SarvaarthN/ESP32_WorldClock_Alarm/PCB/12HrClock_PCB/12HrClock_PCB.kicad_pcb

## KiCad design PCB/12HrClock_PCB/12HrClock_PCB.kicad_pcb (2026-01-28)

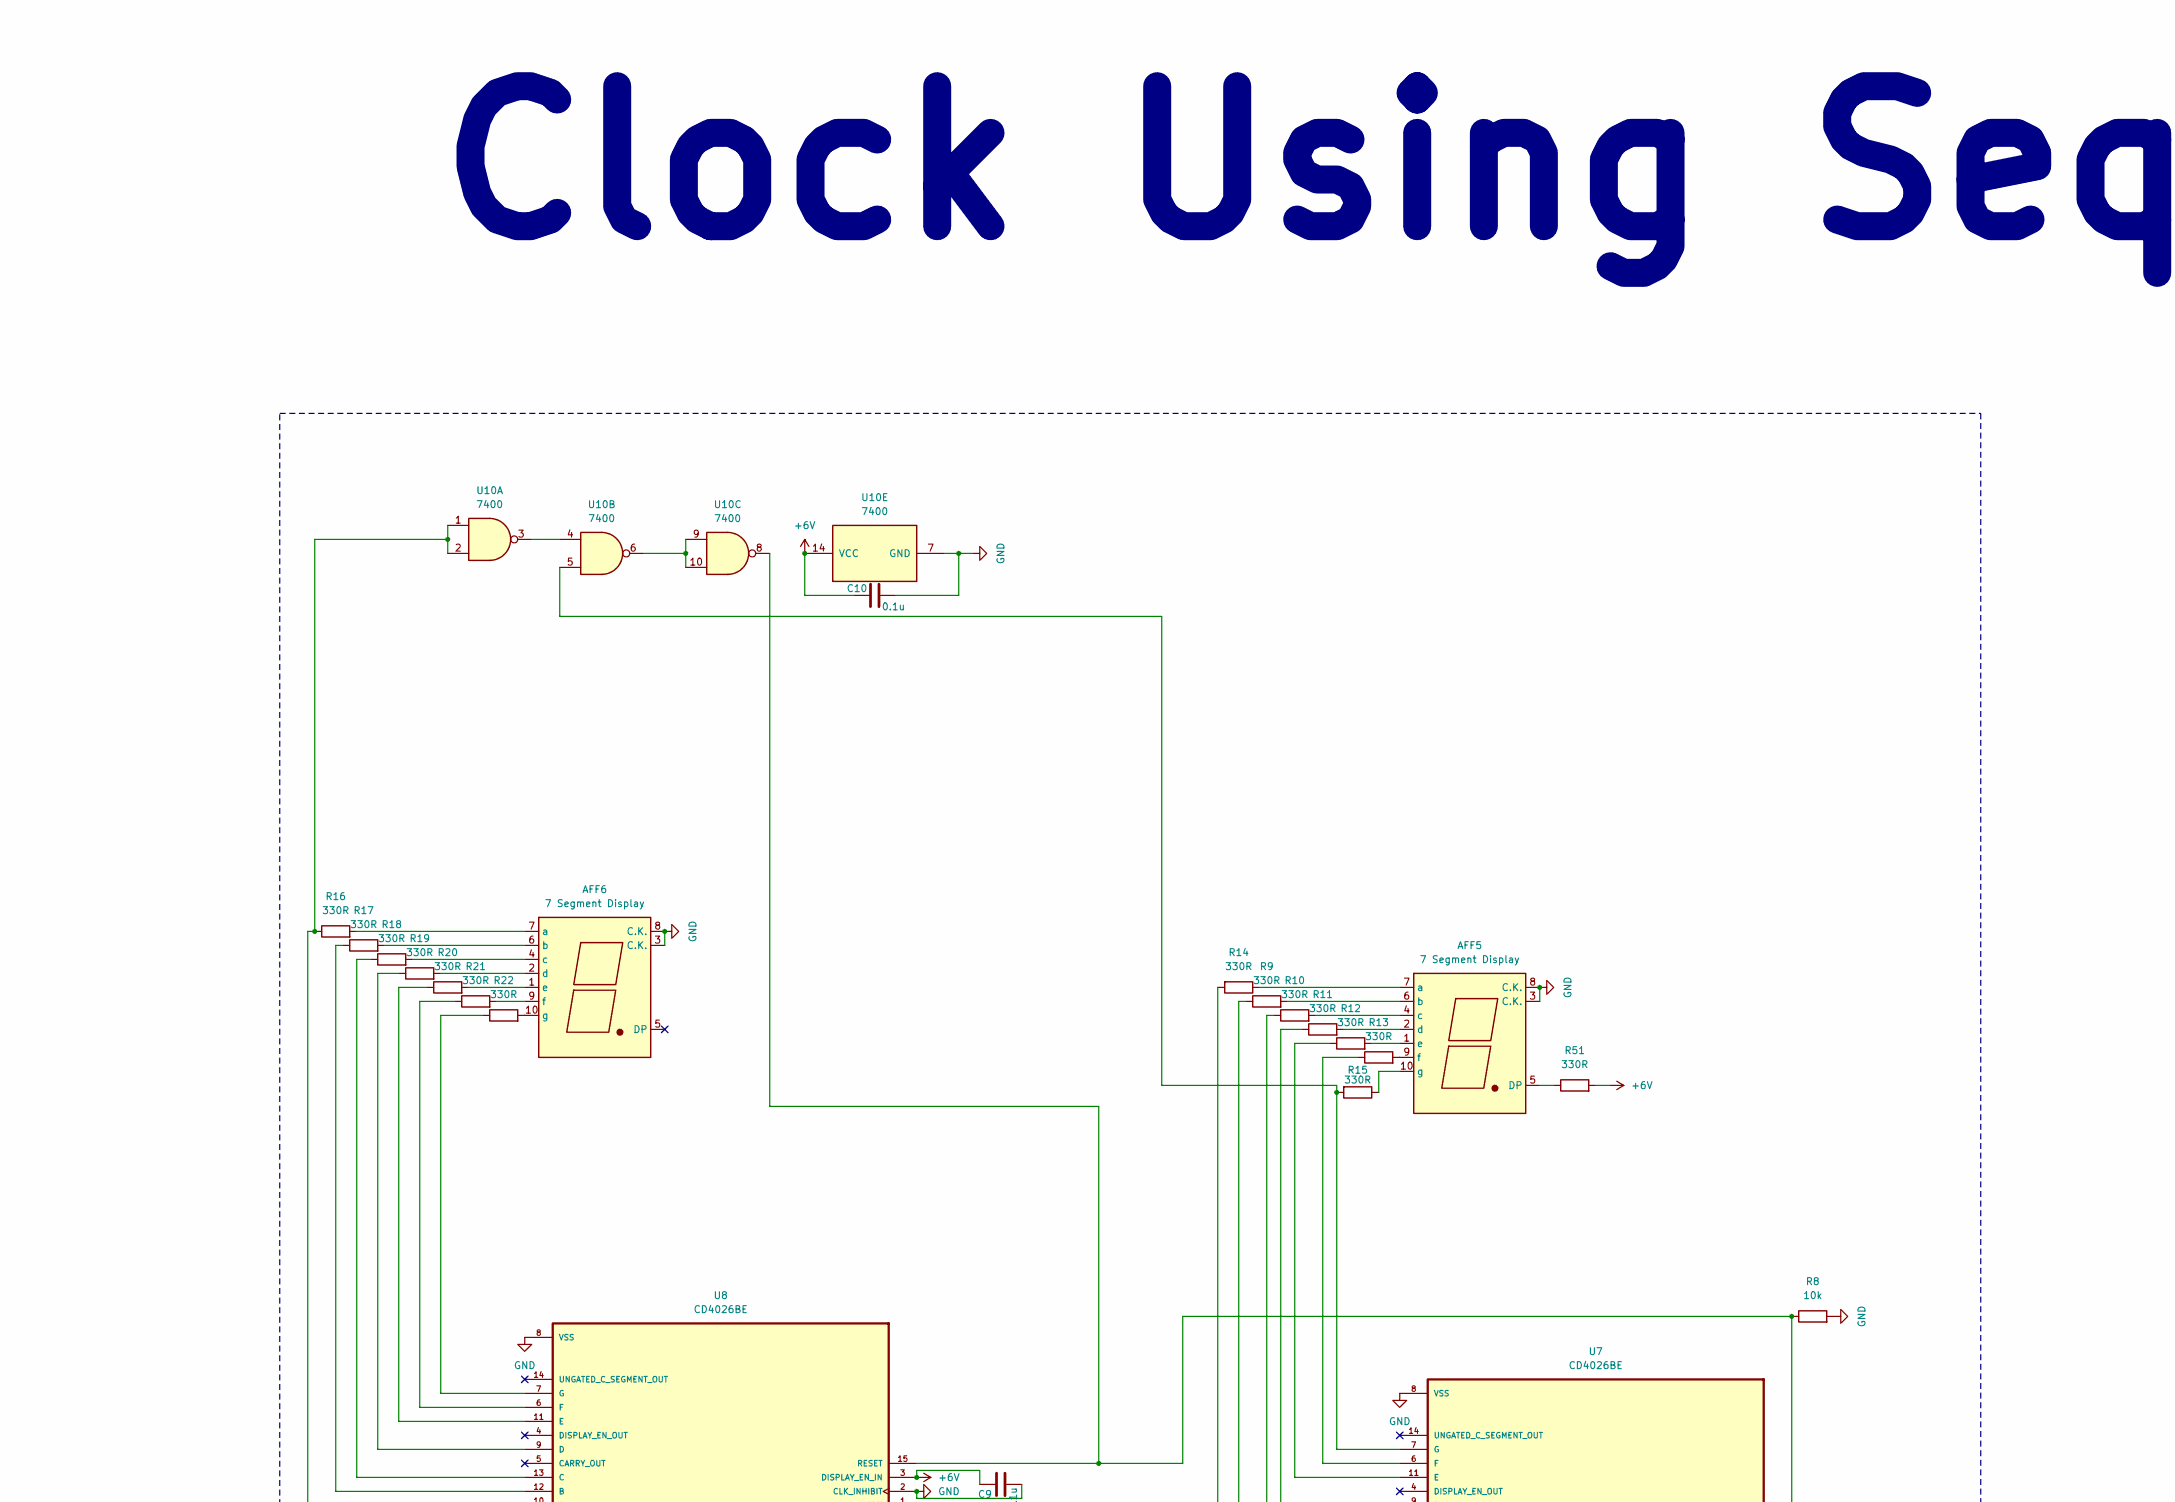
[picture p11: schematic 12HrClock_PCB.kicad_sch, part in row 1, column 1]

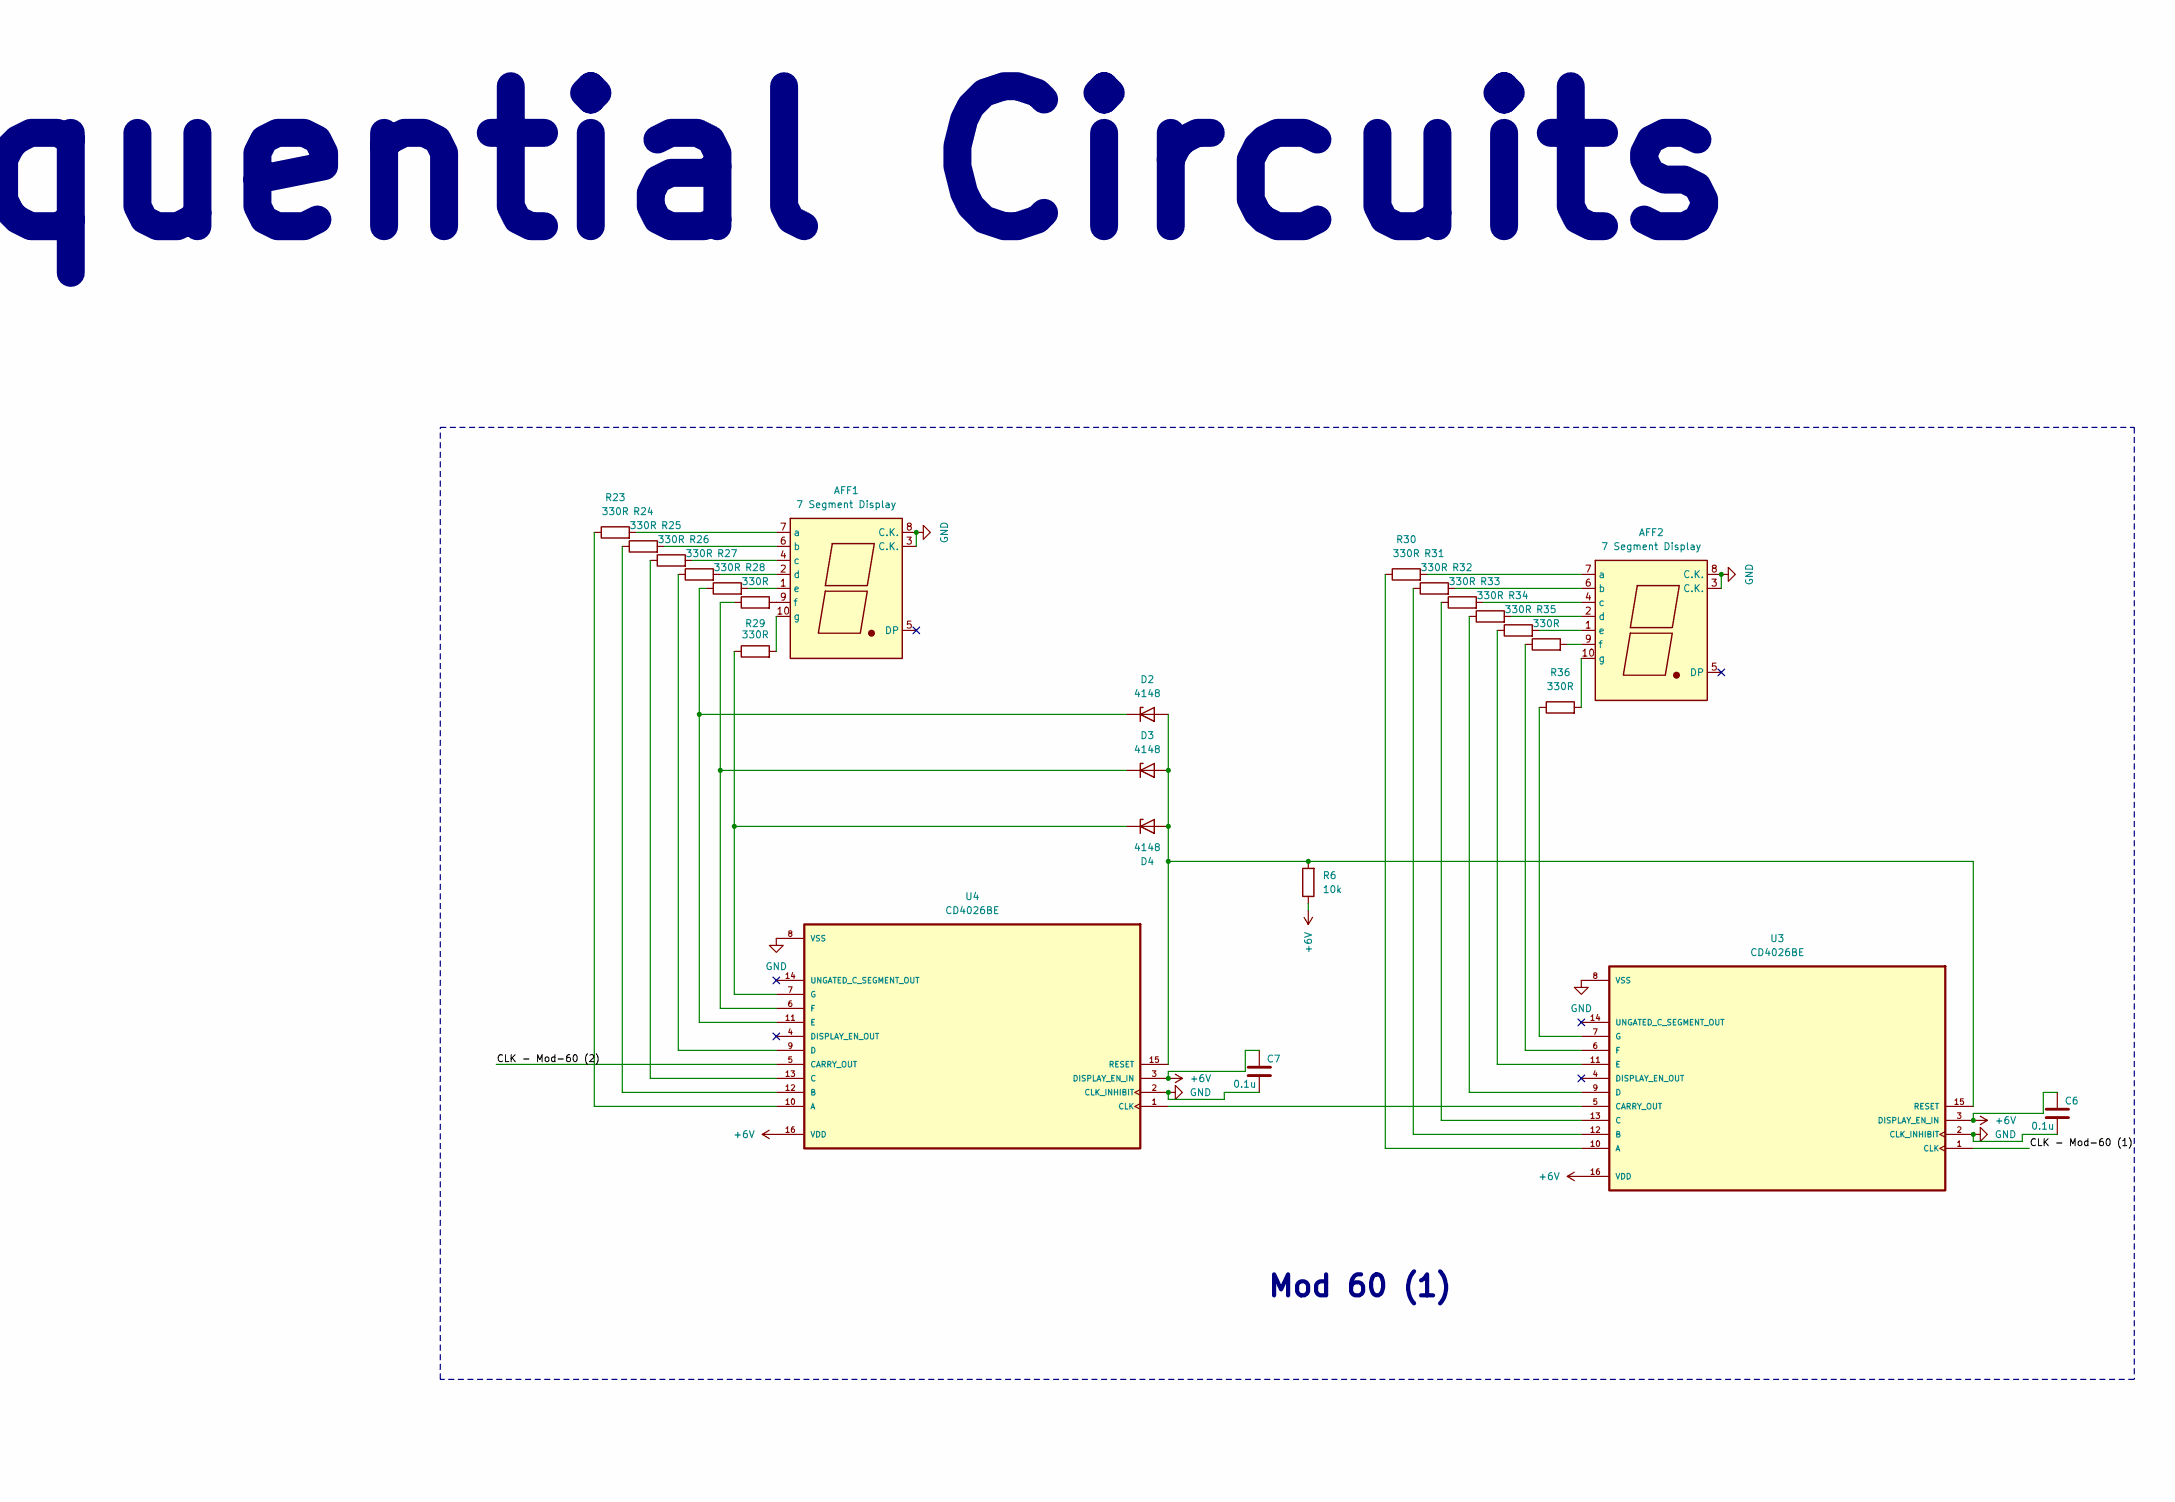
[picture p12: schematic 12HrClock_PCB.kicad_sch, part in row 1, column 2]

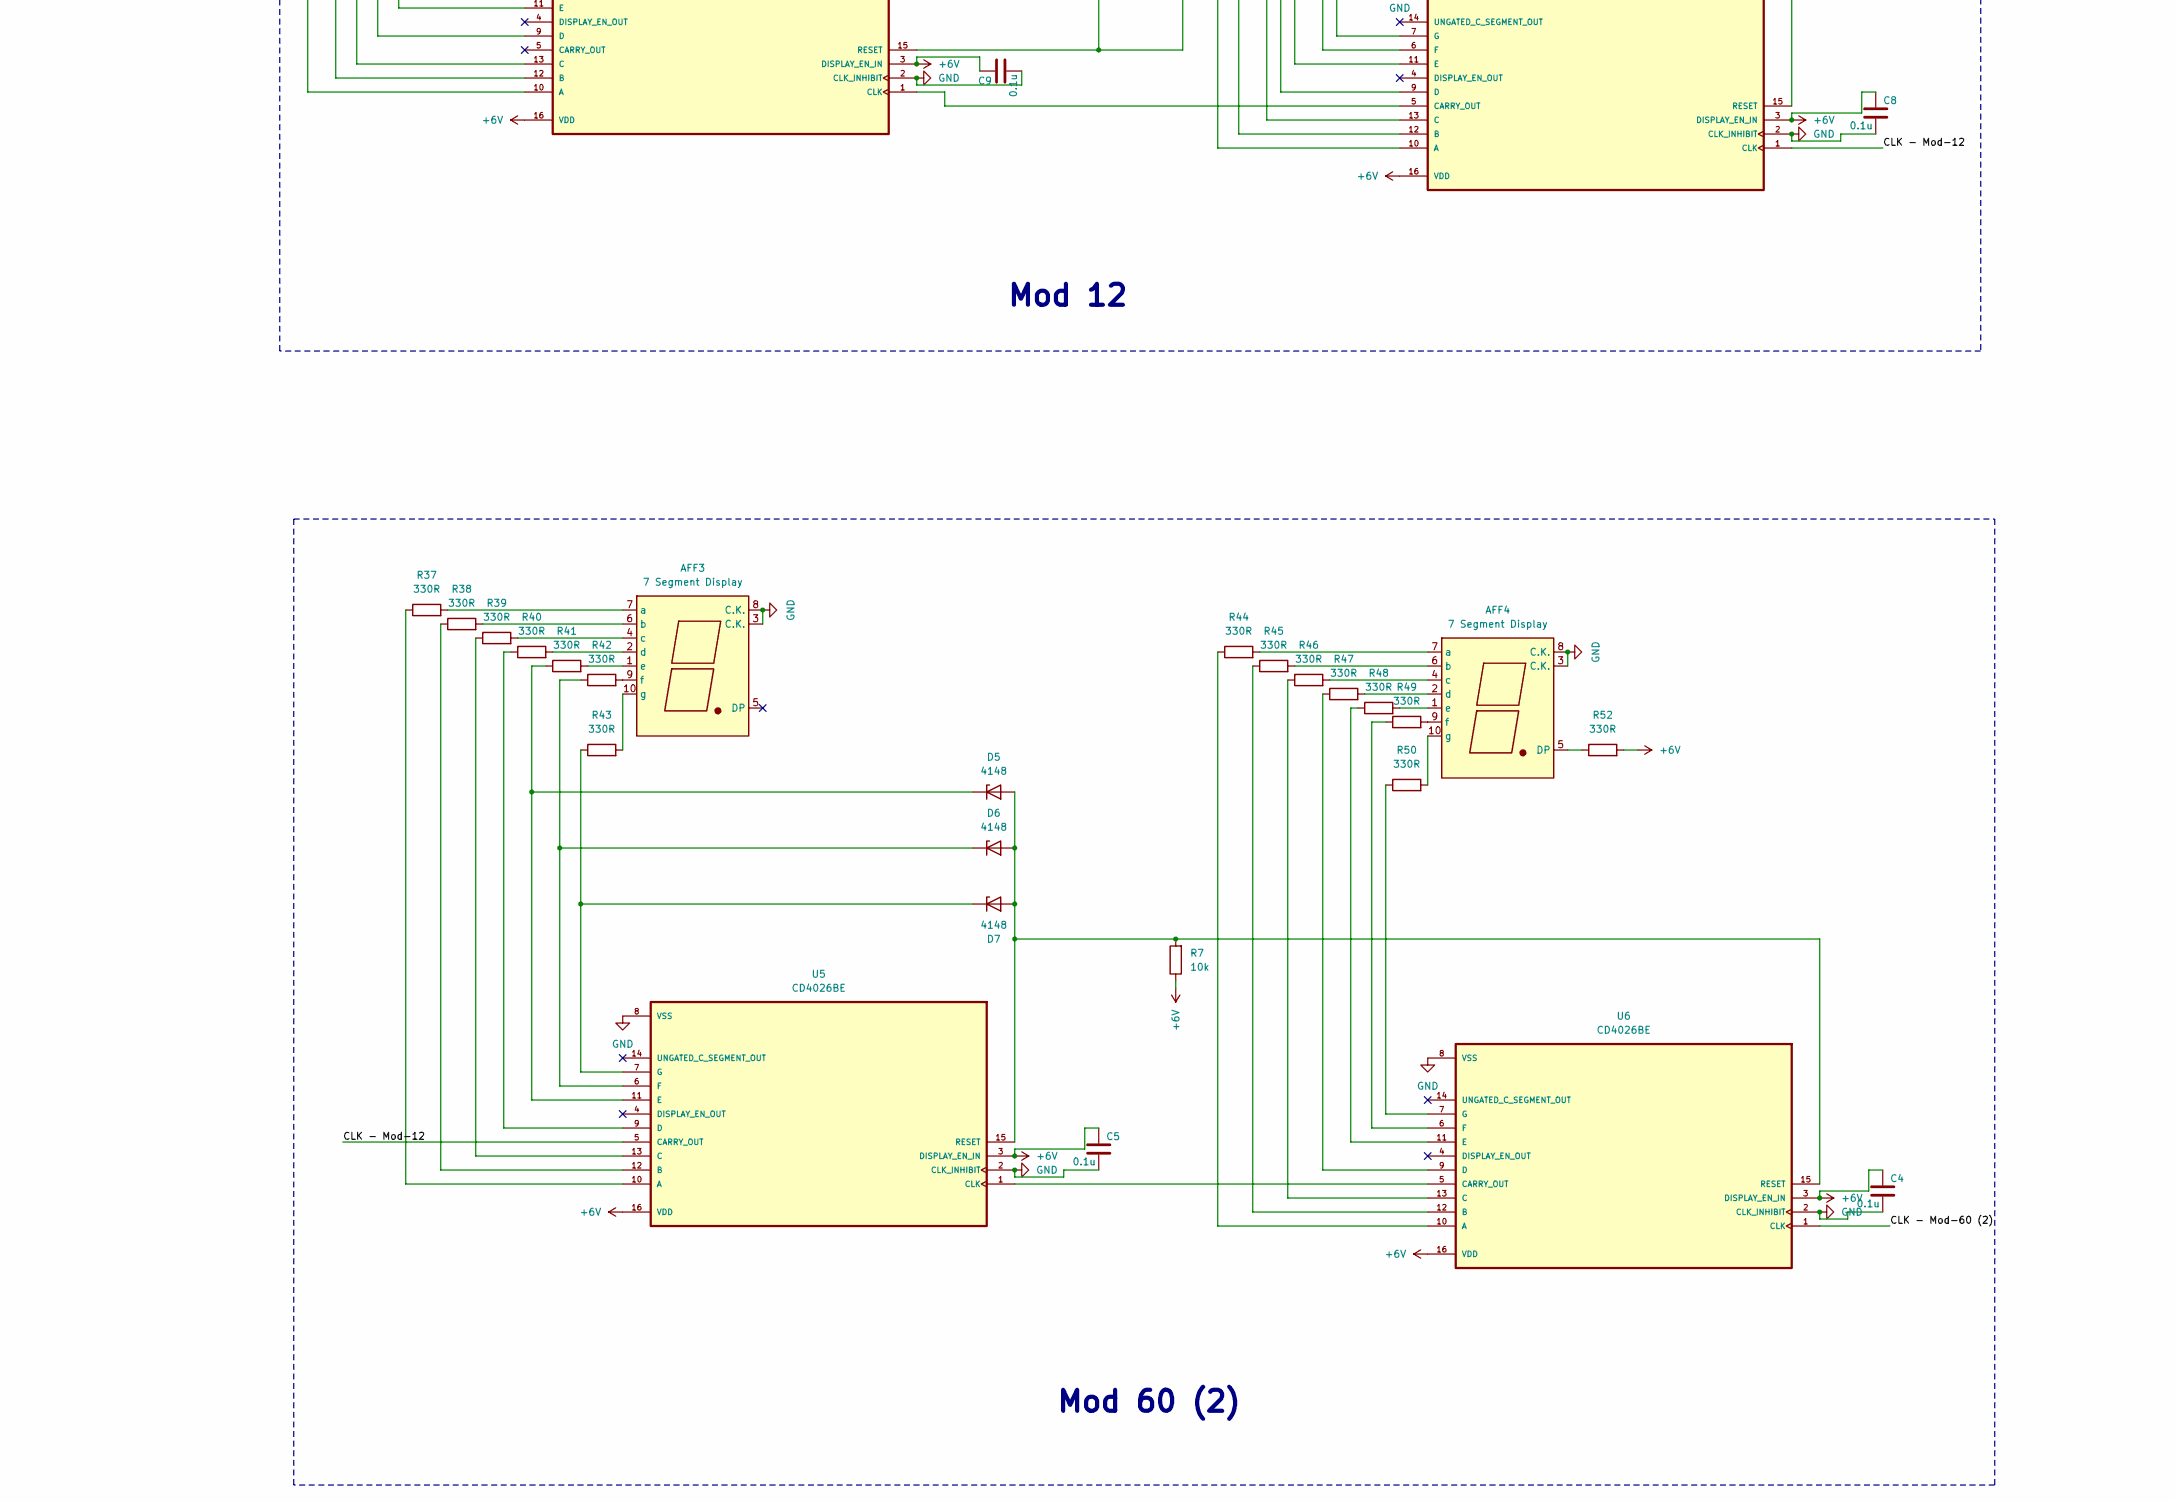
[picture p13: schematic 12HrClock_PCB.kicad_sch, part in row 2, column 1]

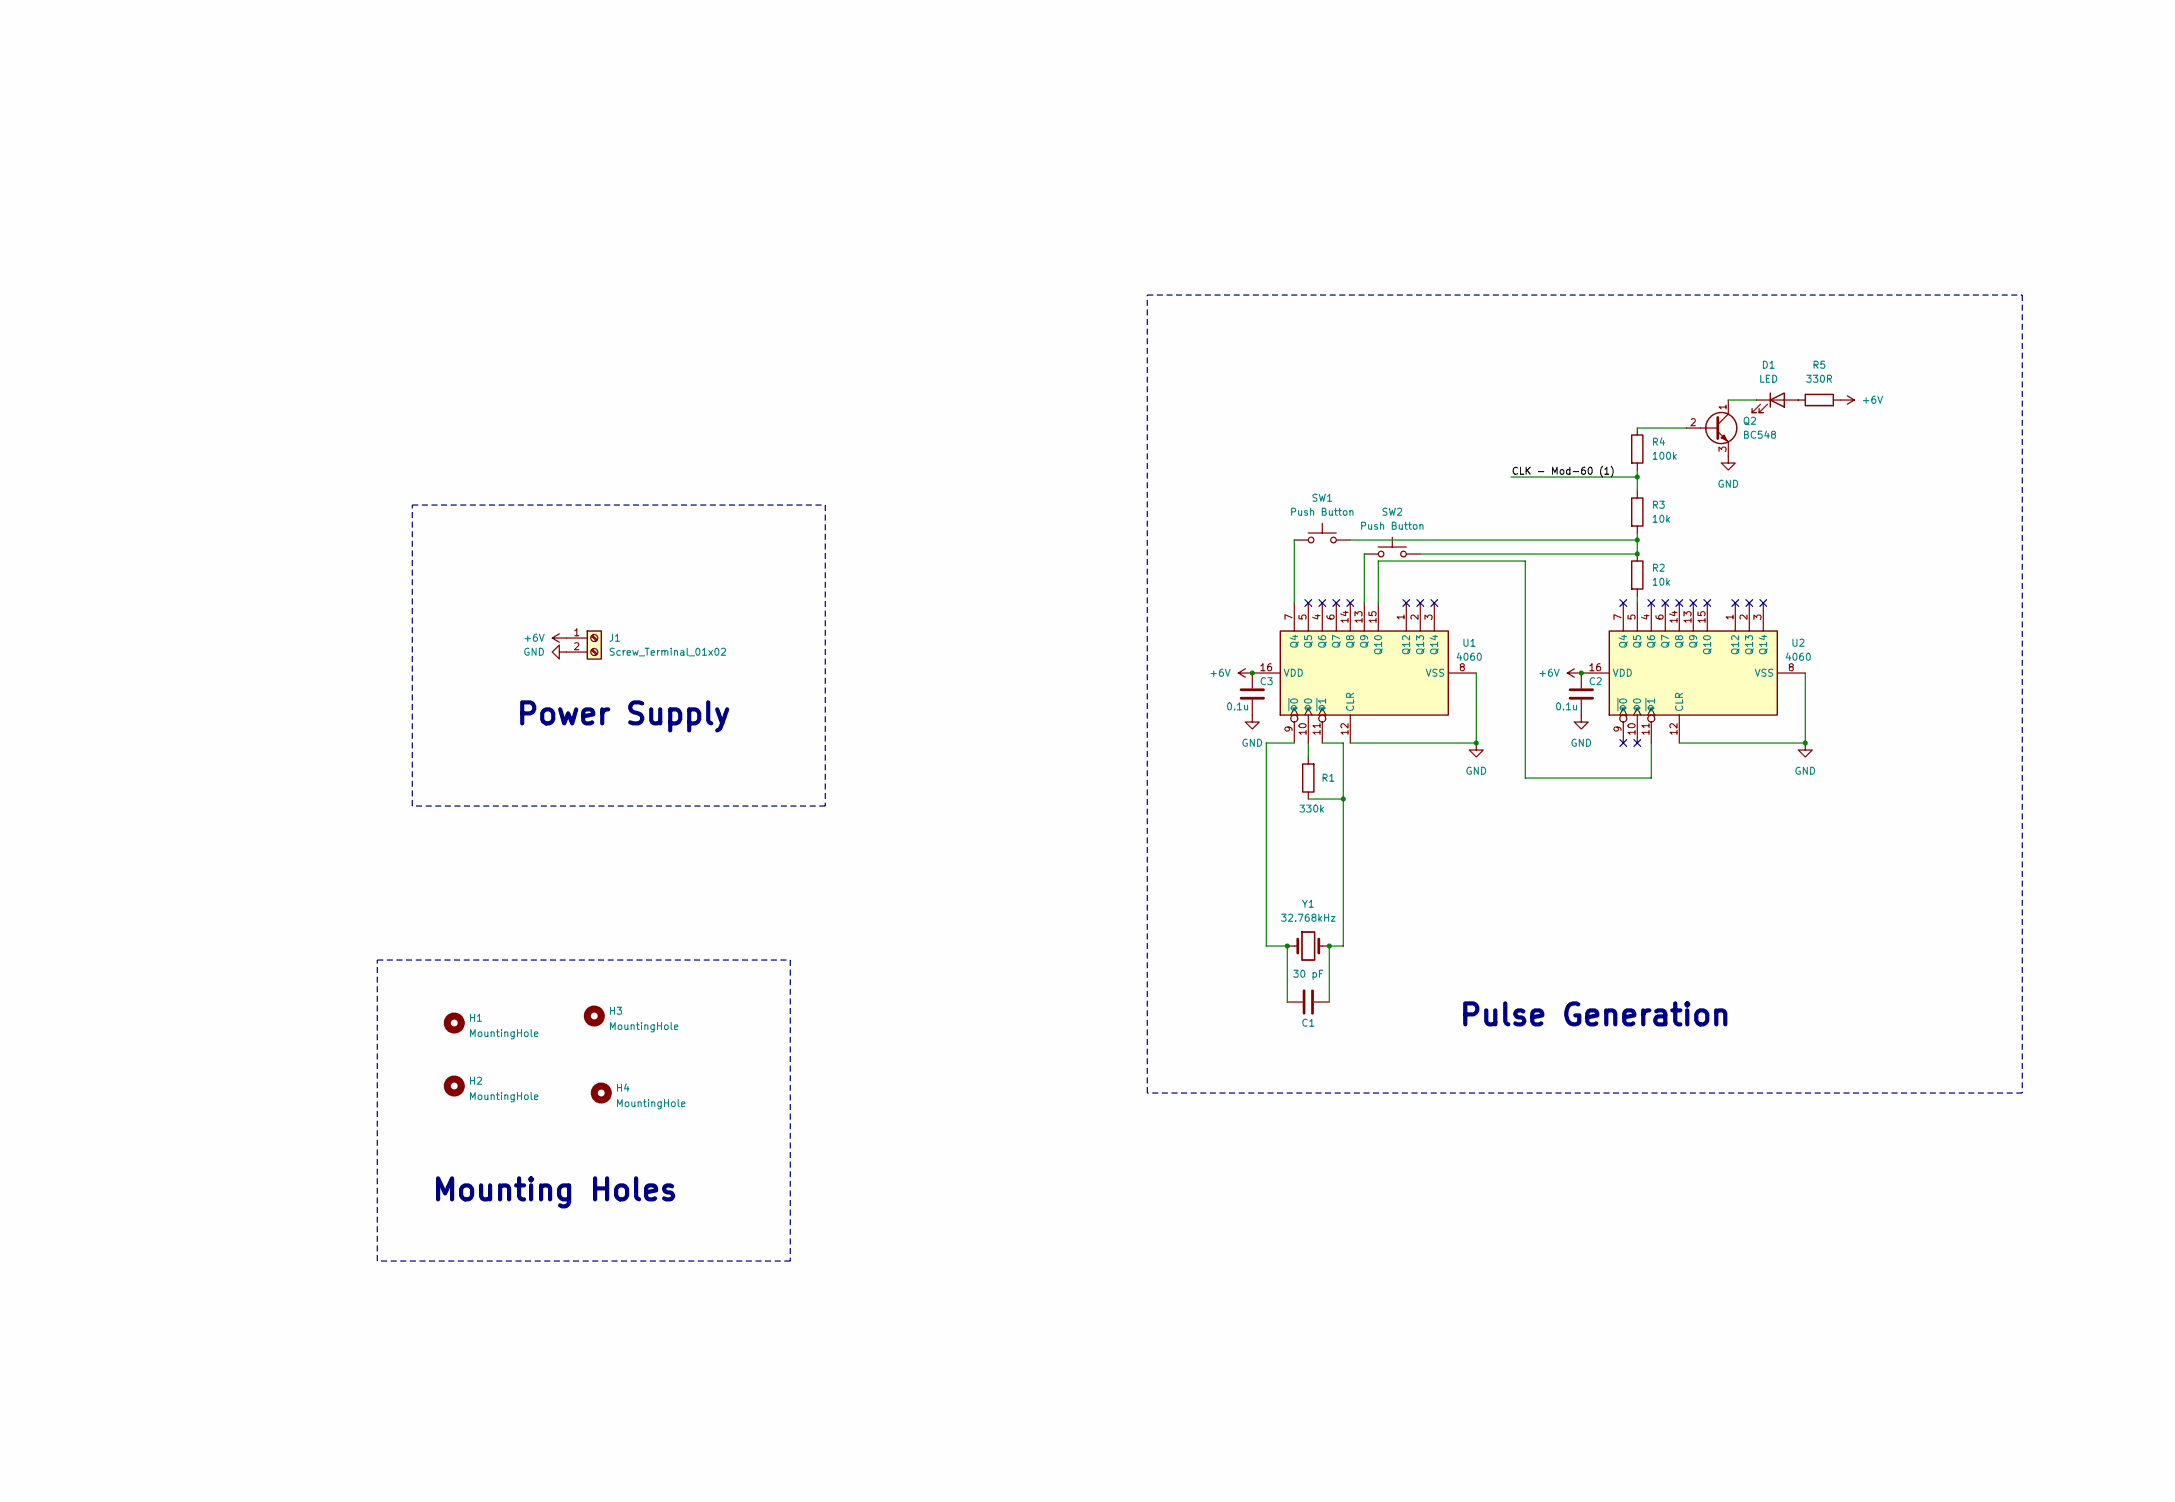
[picture p14: schematic 12HrClock_PCB.kicad_sch, part in row 2, column 2]

Parts:
AFF1, AFF2, AFF3, AFF4, AFF5, AFF6: 7 Segment Display; 7SegmentLED_LTS6760_LTS6780
C1: 30 pF; C_0805_2012Metric_Pad1.18x1.45mm_HandSolder
C2, C3, C4, C5, C6, C7, C8, C9, C10: 0.1u; C_0805_2012Metric_Pad1.18x1.45mm_HandSolder
D1: LED; LED_0805_2012Metric_Pad1.15x1.40mm_HandSolder
D2, D3, D4, D5, D6, D7: 4148; D_DO-35_SOD27_P7.62mm_Horizontal
H1, H2, H3, H4: MountingHole; MountingHole_3.2mm_M3
J1: Screw_Terminal_01x02; TerminalBlock_Phoenix_PT-1,5-2-5.0-H_1x02_P5.00mm_Horizontal
Q2: BC548; TO-92_Inline
R1: 330k; R_0805_2012Metric_Pad1.20x1.40mm_HandSolder
R2, R3, R6, R7, R8: 10k; R_0805_2012Metric_Pad1.20x1.40mm_HandSolder
R4: 100k; R_0805_2012Metric_Pad1.20x1.40mm_HandSolder
R5, R9, R10, R11, R12, R13, R14, R15, R16, R17, R18, R19, R20, R21, R22, R23, R24, R25, R26, R27, R28, R29, R30, R31, R32, R33, R34, R35, R36, R37, R38, R39, R40, R41, R42, R43, R44, R45, R46, R47, R48, R49, R50, R51, R52: 330R; R_0805_2012Metric_Pad1.20x1.40mm_HandSolder
SW1, SW2: Push Button; SW_PUSH_6mm
U1, U2: 4060; DIP-16_W7.62mm_LongPads
U3, U4, U5, U6, U7, U8: CD4026BE; DIP-16_W7.62mm_LongPads
U10: 7400; DIP-14_W7.62mm_LongPads
Y1: 32.768kHz; Crystal_DS10_D1.0mm_L4.3mm_Vertical

Connections:
+6V: C2.1, C3.1, C4.1, C5.1, C6.1, C7.1, C8.1, C9.1, C10.1, J1.1, R5.2, R6.1, R7.1, R51.2, R52.2, U1.16 (VDD), U2.16 (VDD), U3.3 (DISPLAY_EN_IN), U3.16 (VDD), U4.3 (DISPLAY_EN_IN), U4.16 (VDD), U5.3 (DISPLAY_EN_IN), U5.16 (VDD), U6.3 (DISPLAY_EN_IN), U6.16 (VDD), U7.3 (DISPLAY_EN_IN), U7.16 (VDD), U8.3 (DISPLAY_EN_IN), U8.16 (VDD), U10.14 (VCC)
/CLK - Mod-12: U5.5 (CARRY_OUT), U7.1 (CLK)
/CLK - Mod-60 (1): R3.1, R4.2, U3.1 (CLK)
/CLK - Mod-60 (2): U4.5 (CARRY_OUT), U6.1 (CLK)
GND: AFF1.3 (C.K.), AFF1.8 (C.K.), AFF2.3 (C.K.), AFF2.8 (C.K.), AFF3.3 (C.K.), AFF3.8 (C.K.), AFF4.3 (C.K.), AFF4.8 (C.K.), AFF5.3 (C.K.), AFF5.8 (C.K.), AFF6.3 (C.K.), AFF6.8 (C.K.), C2.2, C3.2, C4.2, C5.2, C6.2, C7.2, C8.2, C9.2, C10.2, J1.2, Q2.3 (E), R8.2, U1.8 (VSS), U1.12 (CLR), U2.8 (VSS), U2.12 (CLR), U3.2 (CLK_INHIBIT), U3.8 (VSS), U4.2 (CLK_INHIBIT), U4.8 (VSS), U5.2 (CLK_INHIBIT), U5.8 (VSS), U6.2 (CLK_INHIBIT), U6.8 (VSS), U7.2 (CLK_INHIBIT), U7.8 (VSS), U8.2 (CLK_INHIBIT), U8.8 (VSS), U10.7 (GND)
unnamed: AFF1.7 (a), R23.2
unnamed: AFF1.6 (b), R24.2
unnamed: AFF1.4 (c), R25.2
unnamed: AFF1.2 (d), R26.2
unnamed: AFF1.1 (e), R27.2
unnamed: AFF1.9 (f), R28.2
unnamed: AFF1.10 (g), R29.2
unnamed: AFF2.7 (a), R30.2
unnamed: AFF2.6 (b), R31.2
unnamed: AFF2.4 (c), R32.2
unnamed: AFF2.2 (d), R33.2
unnamed: AFF2.1 (e), R34.2
unnamed: AFF2.9 (f), R35.2
unnamed: AFF2.10 (g), R36.2
unnamed: AFF3.7 (a), R37.2
unnamed: AFF3.6 (b), R38.2
unnamed: AFF3.4 (c), R39.2
unnamed: AFF3.2 (d), R40.2
unnamed: AFF3.1 (e), R41.2
unnamed: AFF3.9 (f), R42.2
unnamed: AFF3.10 (g), R43.2
unnamed: AFF4.5 (DP), R52.1
unnamed: AFF4.7 (a), R44.2
unnamed: AFF4.6 (b), R45.2
unnamed: AFF4.4 (c), R46.2
unnamed: AFF4.2 (d), R47.2
unnamed: AFF4.1 (e), R48.2
unnamed: AFF4.9 (f), R49.2
unnamed: AFF4.10 (g), R50.2
unnamed: AFF5.5 (DP), R51.1
unnamed: AFF5.7 (a), R14.1
unnamed: AFF5.6 (b), R9.2
unnamed: AFF5.4 (c), R10.2
unnamed: AFF5.2 (d), R11.2
unnamed: AFF5.1 (e), R12.2
unnamed: AFF5.9 (f), R13.2
unnamed: AFF5.10 (g), R15.1
unnamed: AFF6.7 (a), R16.2
unnamed: AFF6.6 (b), R17.2
unnamed: AFF6.4 (c), R18.2
unnamed: AFF6.2 (d), R19.2
unnamed: AFF6.1 (e), R20.2
unnamed: AFF6.9 (f), R21.2
unnamed: AFF6.10 (g), R22.2
unnamed: D1.2 (A), R5.1
unnamed: D1.1 (K), Q2.1 (C)
unnamed: D2.2 (A), D3.2 (A), D4.2 (A), R6.2, U3.15 (RESET), U4.15 (RESET)
unnamed: D2.1 (K), R27.1, U4.11 (E)
unnamed: D3.1 (K), R28.1, U4.6 (F)
unnamed: D4.1 (K), R29.1, U4.7 (G)
unnamed: D5.2 (A), D6.2 (A), D7.2 (A), R7.2, U5.15 (RESET), U6.15 (RESET)
unnamed: D5.1 (K), R41.1, U5.11 (E)
unnamed: D6.1 (K), R42.1, U5.6 (F)
unnamed: D7.1 (K), R43.1, U5.7 (G)
unnamed: Q2.2 (B), R4.1
unnamed: R2.1, R3.2, SW1.2, SW2.2
unnamed: SW1.1, U1.7 (Q4)
unnamed: SW2.1, U1.13 (Q9)
unnamed: U1.15 (Q10), U2.11 (~Φ1)
unnamed: C1.1, U1.9 (~Φ0), Y1.1
unnamed: C1.2, R1.1, U1.11 (~Φ1), Y1.2
unnamed: R1.2, U1.10 (Φ0)
unnamed: R2.2, U2.5 (Q5)
unnamed: R30.1, U3.10 (A)
unnamed: R31.1, U3.12 (B)
unnamed: R32.1, U3.13 (C)
unnamed: U3.5 (CARRY_OUT), U4.1 (CLK)
unnamed: R33.1, U3.9 (D)
unnamed: R34.1, U3.11 (E)
unnamed: R35.1, U3.6 (F)
unnamed: R36.1, U3.7 (G)
unnamed: R23.1, U4.10 (A)
unnamed: R24.1, U4.12 (B)
unnamed: R25.1, U4.13 (C)
unnamed: R26.1, U4.9 (D)
unnamed: R37.1, U5.10 (A)
unnamed: R38.1, U5.12 (B)
unnamed: R39.1, U5.13 (C)
unnamed: U5.1 (CLK), U6.5 (CARRY_OUT)
unnamed: R40.1, U5.9 (D)
unnamed: R44.1, U6.10 (A)
unnamed: R45.1, U6.12 (B)
unnamed: R46.1, U6.13 (C)
unnamed: R47.1, U6.9 (D)
unnamed: R48.1, U6.11 (E)
unnamed: R49.1, U6.6 (F)
unnamed: R50.1, U6.7 (G)
unnamed: R14.2, U7.10 (A)
unnamed: R9.1, U7.12 (B)
unnamed: R10.1, U7.13 (C)
unnamed: U7.5 (CARRY_OUT), U8.1 (CLK)
unnamed: R11.1, U7.9 (D)
unnamed: R12.1, U7.11 (E)
unnamed: R13.1, U7.6 (F)
unnamed: R15.2, U7.7 (G), U10.5
unnamed: R8.1, U7.15 (RESET), U8.15 (RESET), U10.8
unnamed: R16.1, U8.10 (A), U10.1, U10.2
unnamed: R17.1, U8.12 (B)
unnamed: R18.1, U8.13 (C)
unnamed: R19.1, U8.9 (D)
unnamed: R20.1, U8.11 (E)
unnamed: R21.1, U8.6 (F)
unnamed: R22.1, U8.7 (G)
unnamed: U10.3, U10.4
unnamed: U10.6, U10.9, U10.10

Notes on the sheet:
Pulse Generation
Mod 60 (1)
Power Supply
Mounting Holes
Clock Using Sequential Circuits
Mod 60 (2)
Mod 12

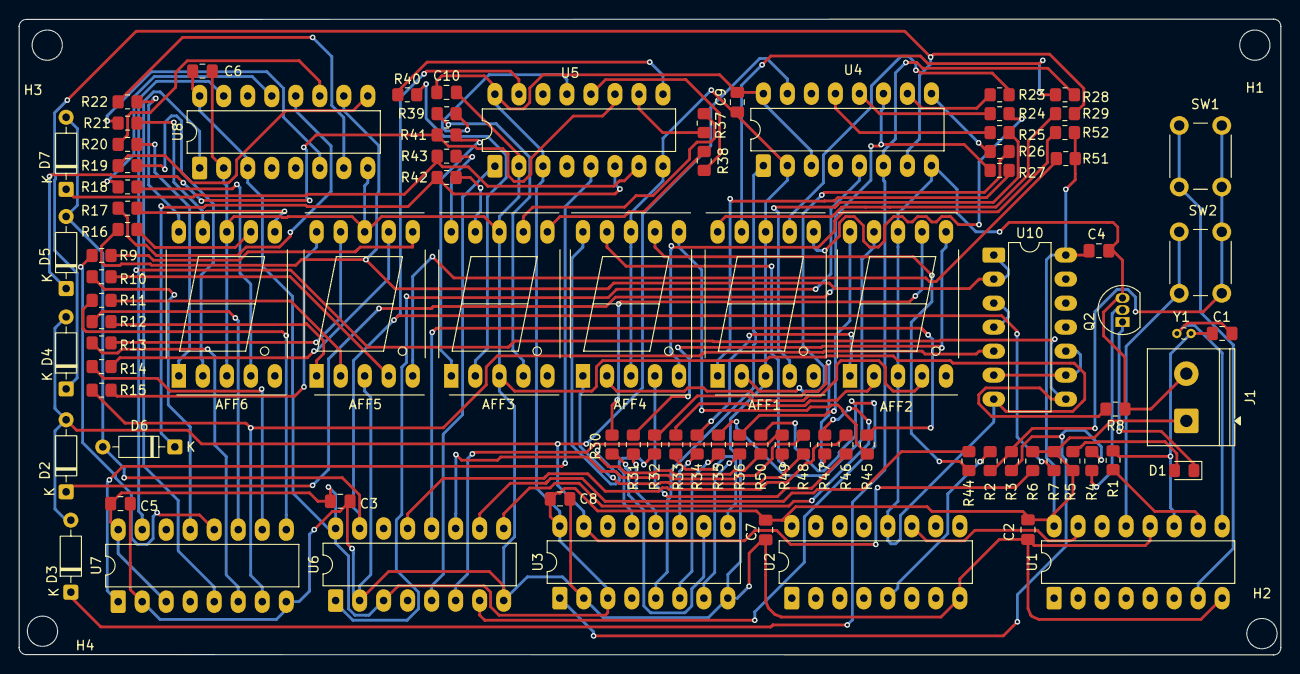
[picture p15: board 12HrClock_PCB.kicad_pcb from above]

Board: 2 copper layers, 133.5 x 67.2 mm, 93 parts (0 on the bottom side), 110 nets.
